ThunderFly-aerospace/TF-AEROSCALE/CAD/png/888_1001.png

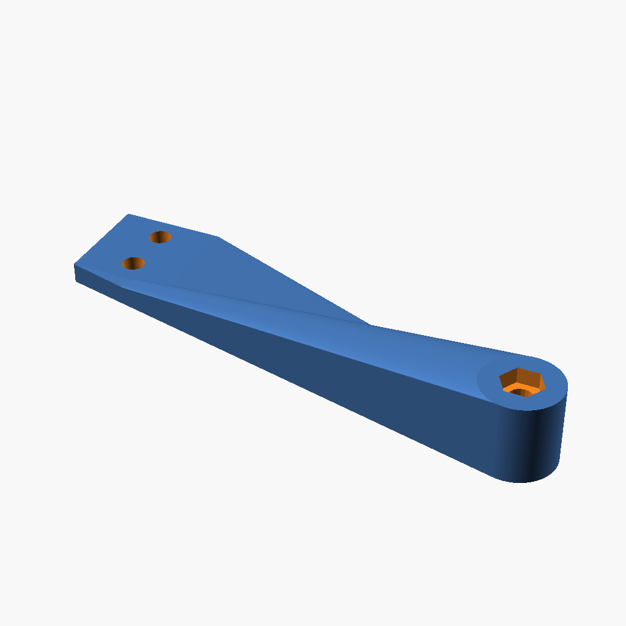
CAD/png/888_1001.png
