ThunderFly-aerospace/TF-AEROSCALE/CAD/png/888_1002.png

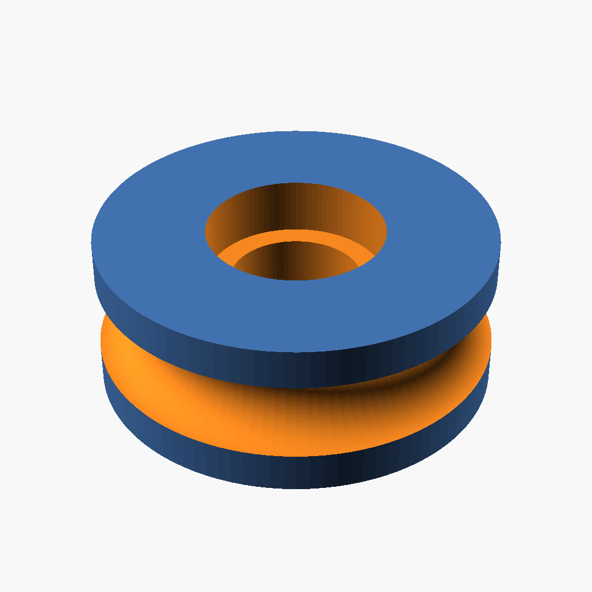
CAD/png/888_1002.png
