ThunderFly-aerospace/TF-AEROSCALE/CAD/png/888_3007.png

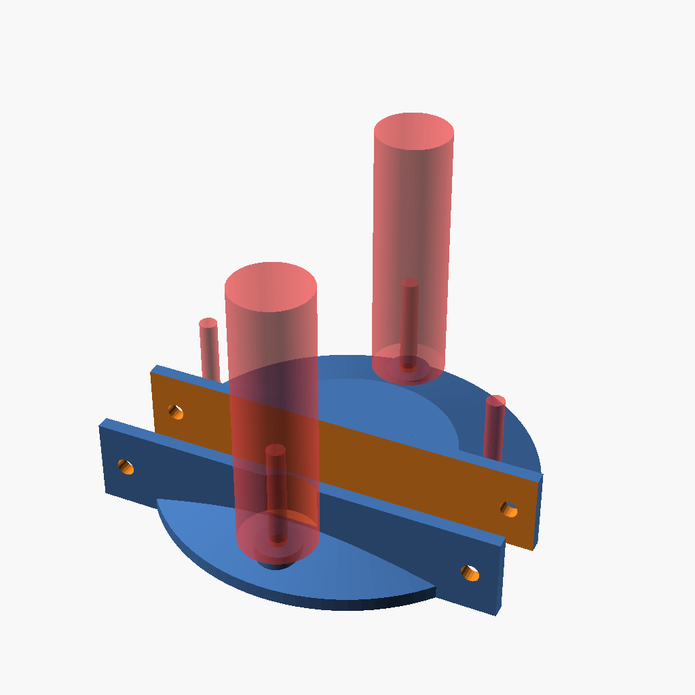
CAD/png/888_3007.png
