ThunderFly-aerospace/TF-AEROSCALE/CAD/png/888_5001.png

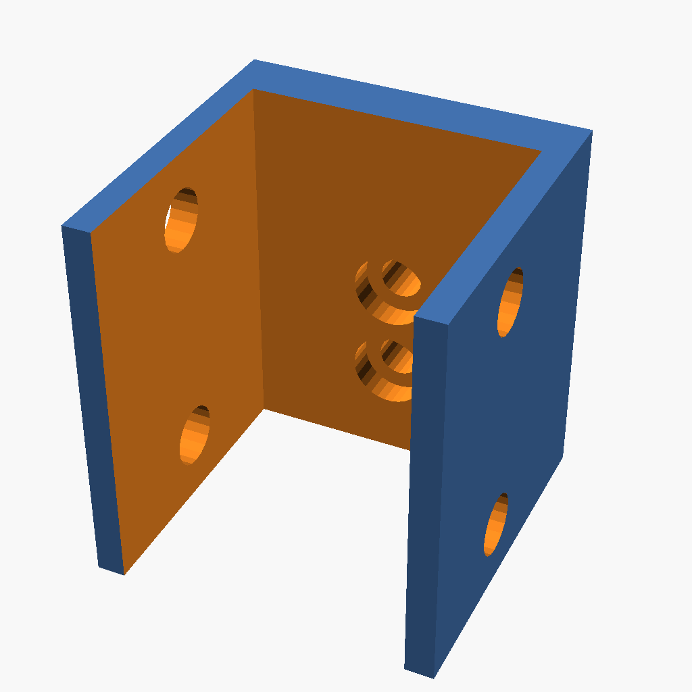
CAD/png/888_5001.png
