ThunderFly-aerospace/TF-AEROSCALE/CAD/png/888_5002.png

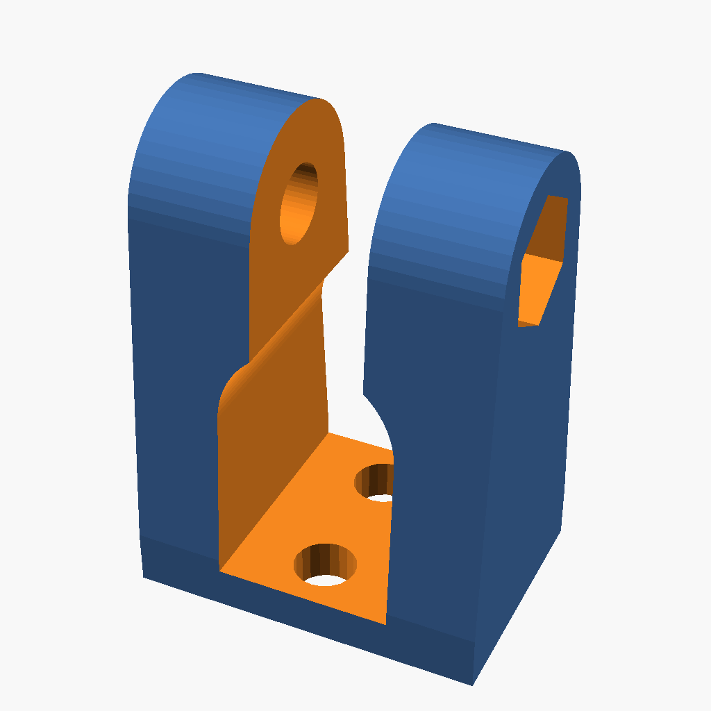
CAD/png/888_5002.png
