ThunderFly-aerospace/TF-AEROSCALE/CAD/png/888_5004.png

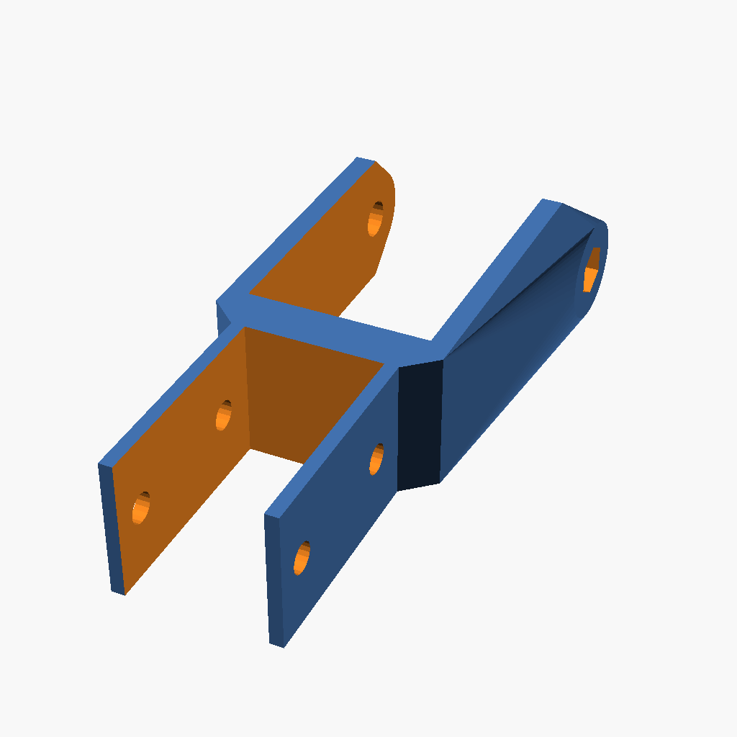
CAD/png/888_5004.png
