ThunderFly-aerospace/TF-AEROSCALE/CAD/png/888_5005.png

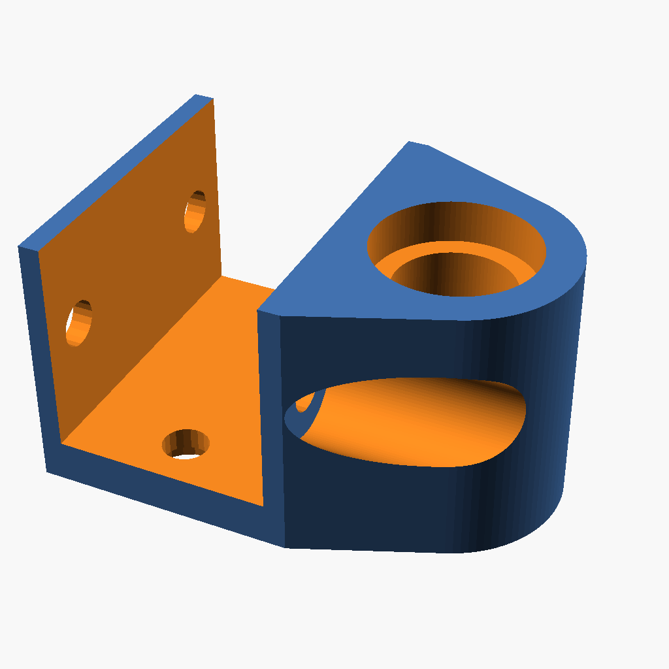
CAD/png/888_5005.png
