ThunderFly-aerospace/TF-AEROSCALE/CAD/png/888_5006.png

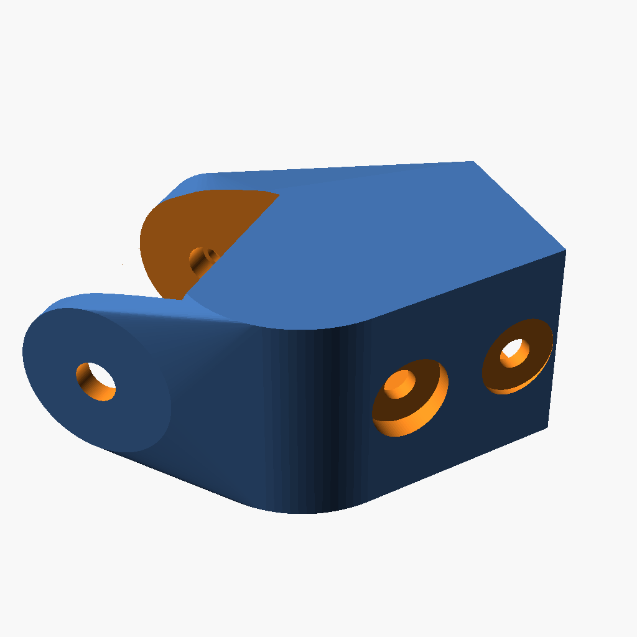
CAD/png/888_5006.png
