ThunderFly-aerospace/TF-AEROSCALE/CAD/png/888_5007.png

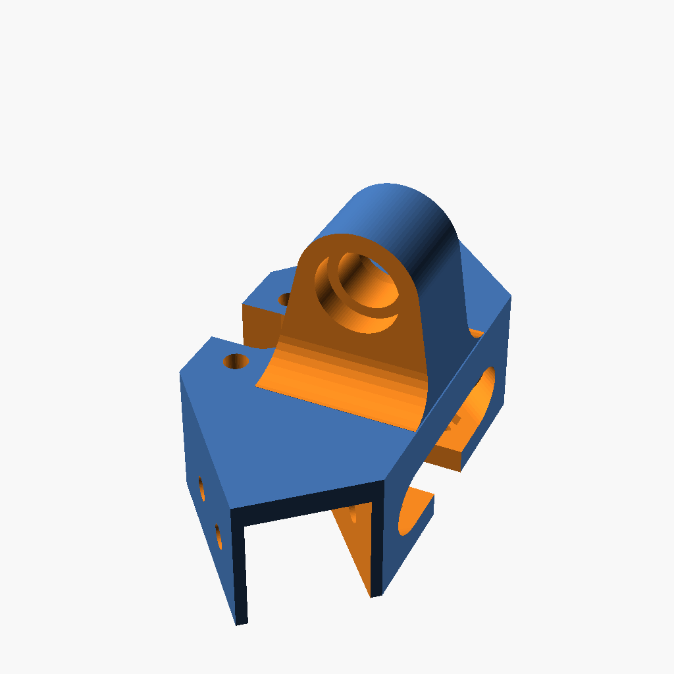
CAD/png/888_5007.png
