ThunderFly-aerospace/TF-AEROSCALE/CAD/png/888_5008.png

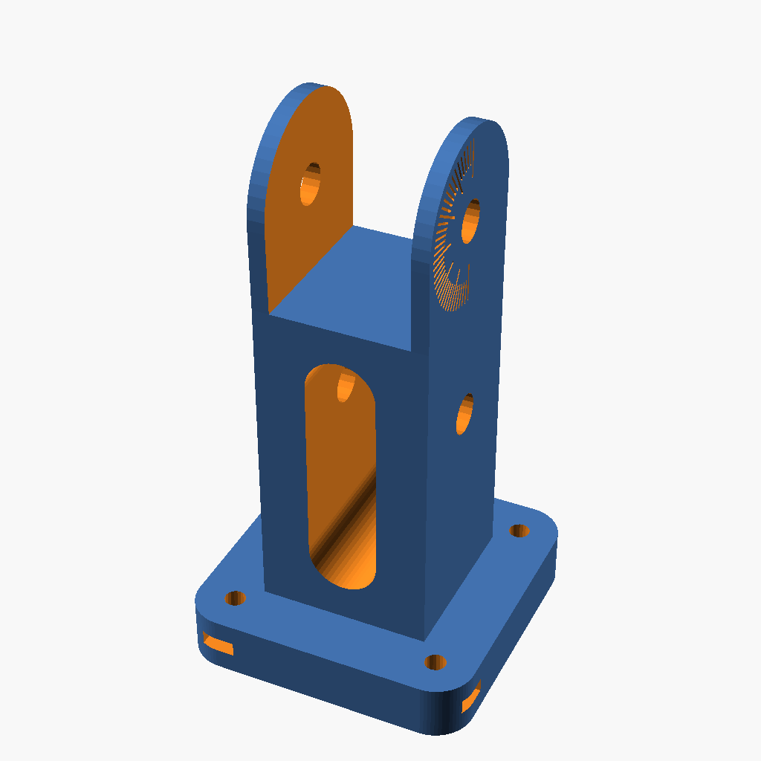
CAD/png/888_5008.png
