ThunderFly-aerospace/TF-AEROSCALE/CAD/png/888_5009.png

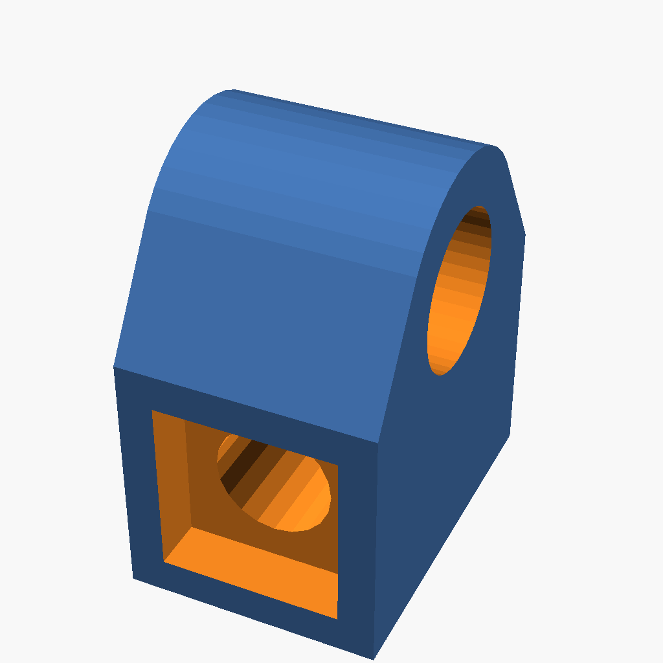
CAD/png/888_5009.png
