ThunderFly-aerospace/TF-AEROSCALE/CAD/png/888_5010.png

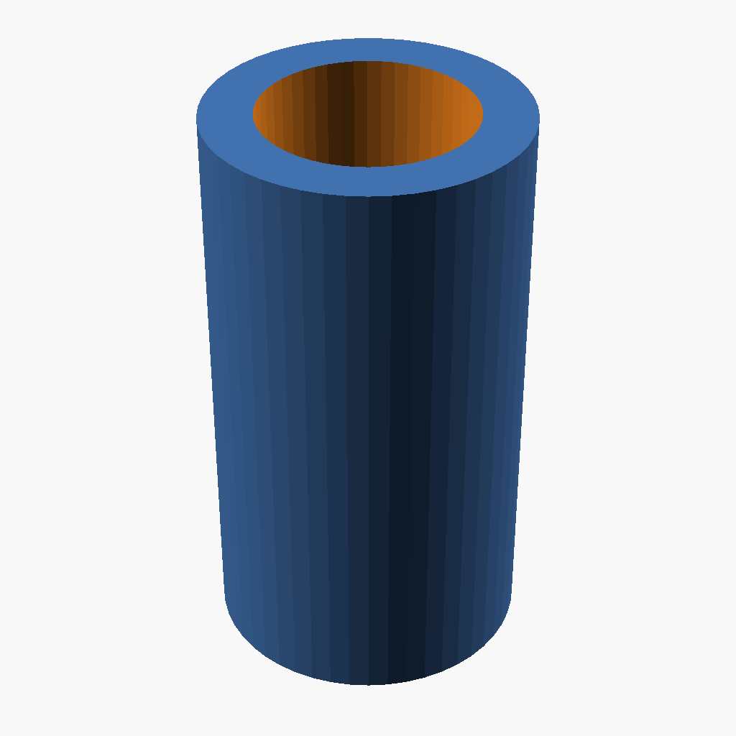
CAD/png/888_5010.png
