ThunderFly-aerospace/TF-AEROSCALE/CAD/png/888_5011.png

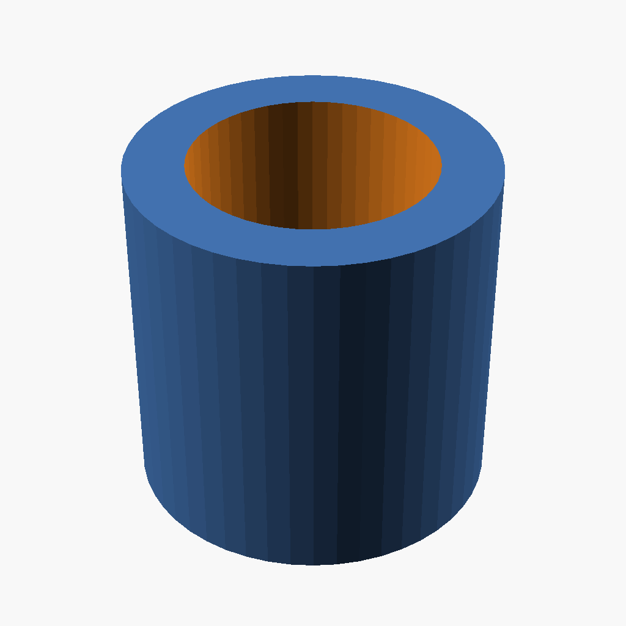
CAD/png/888_5011.png
