ThunderFly-aerospace/TF-AEROSCALE/CAD/png/888_5013.png

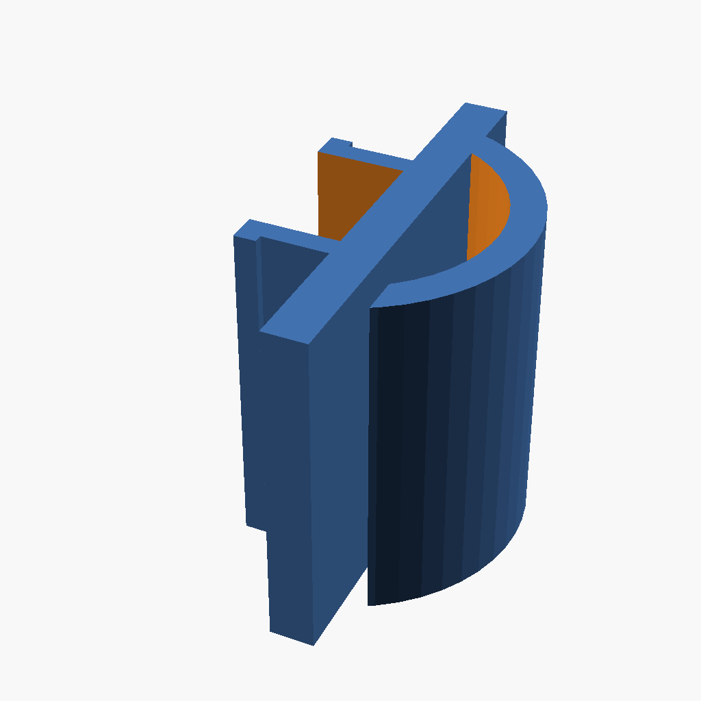
CAD/png/888_5013.png
