ThunderFly-aerospace/TF-AEROSCALE/CAD/png/888_5014_Front.png

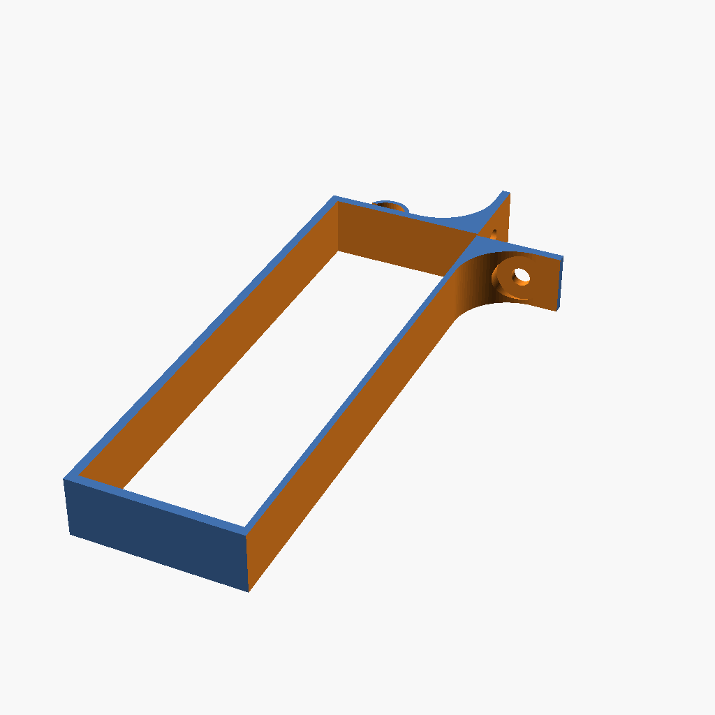
CAD/png/888_5014_Front.png
