ThunderFly-aerospace/TF-AEROSCALE/CAD/png/888_5015.png

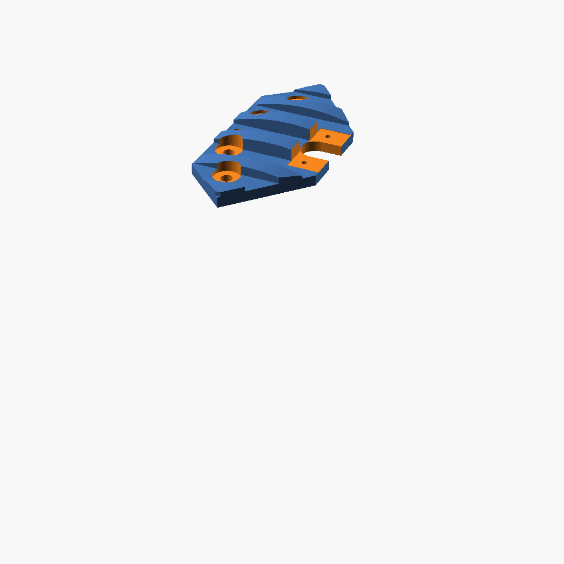
CAD/png/888_5015.png
