ThunderFly-aerospace/TF-AEROSCALE/CAD/amf/888_5012.amf

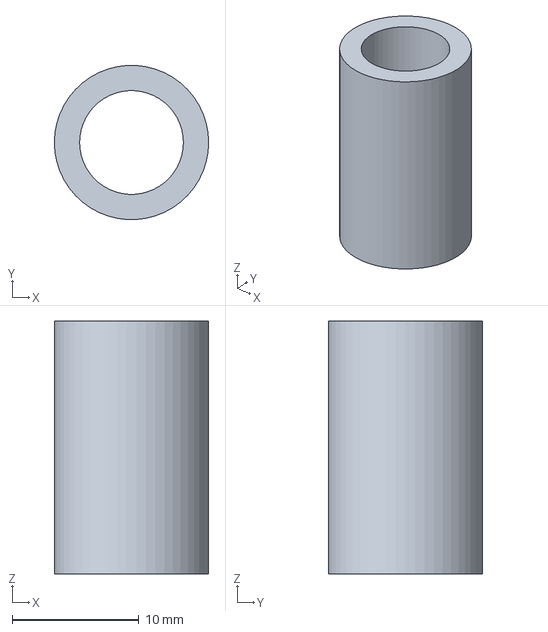
[picture p38: CAD file, 2021-09-10]
CAD/amf/888_5012.amf
12.2 x 12.2 x 20.0 mm
