ThunderFly-aerospace/TF-AEROSCALE/CAD/amf/888_5014_Back.amf

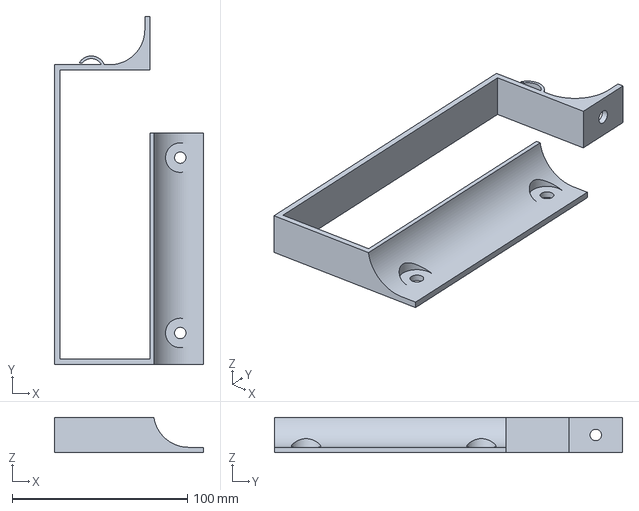
[picture p39: CAD file, 2021-09-10]
CAD/amf/888_5014_Back.amf
85.0 x 198.5 x 20.0 mm
