ThunderFly-aerospace/TF-AEROSCALE/CAD/amf/888_5010.amf

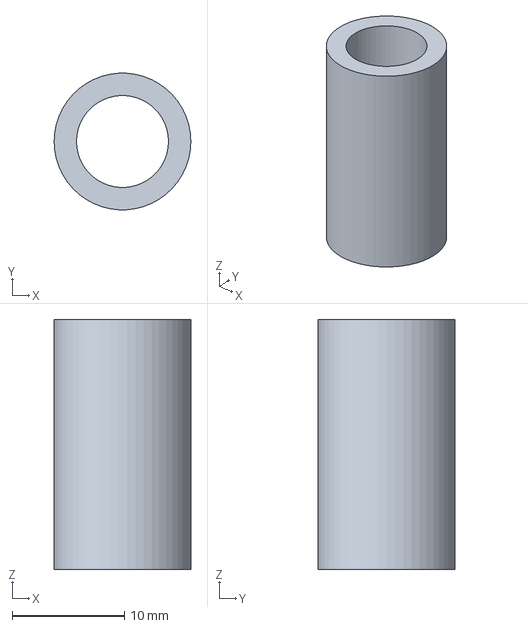
[picture p40: CAD file, 2021-09-10]
CAD/amf/888_5010.amf
12.2 x 12.2 x 22.3 mm
