ThunderFly-aerospace/TF-AEROSCALE/CAD/amf/888_5003_A.amf

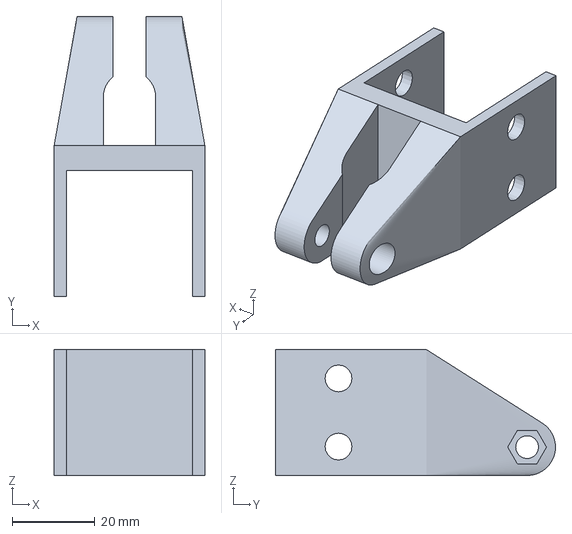
[picture p41: CAD file, 2021-09-10]
CAD/amf/888_5003_A.amf
36.5 x 67.8 x 30.5 mm
