ThunderFly-aerospace/TF-AEROSCALE/CAD/amf/888_1002.amf

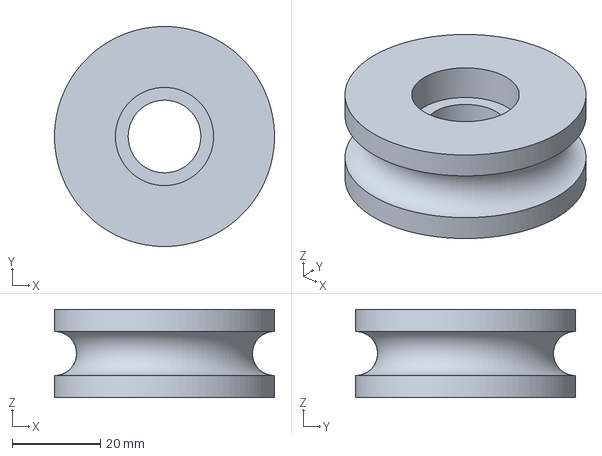
[picture p42: CAD file, 2021-09-10]
CAD/amf/888_1002.amf
50.0 x 50.0 x 20.0 mm
