ThunderFly-aerospace/TF-AEROSCALE/CAD/amf/888_1003.amf

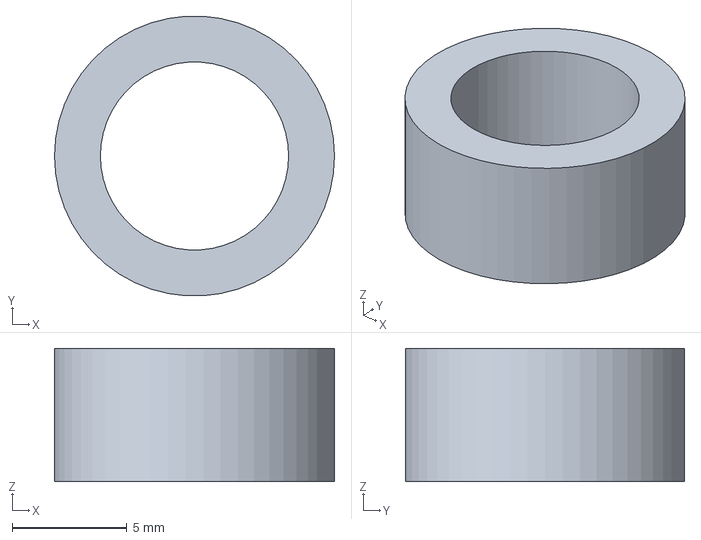
[picture p43: CAD file, 2021-09-10]
CAD/amf/888_1003.amf
12.2 x 12.2 x 5.80 mm
