ThunderFly-aerospace/TF-AEROSCALE/CAD/amf/888_5011.amf

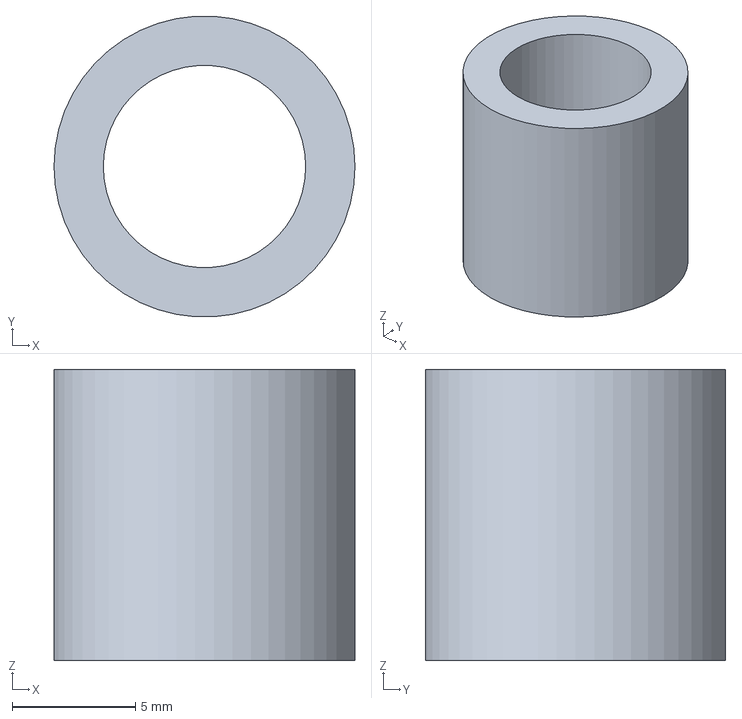
[picture p44: CAD file, 2021-09-10]
CAD/amf/888_5011.amf
12.2 x 12.2 x 11.8 mm
