ThunderFly-aerospace/TF-AEROSCALE/CAD/print_plates/888_1002.scad

//@set_slicing_config(../slicing/default.ini)

include <../parameters.scad>
use <../src/888_1002.scad>

888_1002(print_plate=true);
