ThunderFly-aerospace/TF-AEROSCALE/CAD/print_plates/888_3007.scad

//@set_slicing_config(../slicing/default.ini)

include <../parameters.scad>
use <../src/888_3007.scad>

888_3007();
