ThunderFly-aerospace/TF-AEROSCALE/CAD/print_plates/888_5002.scad

//@set_slicing_config(../slicing/default.ini)

include <../parameters.scad>
use <../src/888_5002.scad>

translate([0, 0, 4])
888_5002();
