ThunderFly-aerospace/TF-AEROSCALE/CAD/print_plates/888_5003_A.scad

//@set_slicing_config(../slicing/default.ini)

include <../parameters.scad>
use <../src/888_5003.scad>

888_5003_A();
