ThunderFly-aerospace/TF-AEROSCALE/CAD/print_plates/888_5005.scad

//@set_slicing_config(../slicing/default.ini)

include <../parameters.scad>
use <../src/888_5005.scad>

rotate([-90, 0, 0])
888_5005(true);
