ThunderFly-aerospace/TF-AEROSCALE/CAD/print_plates/888_5008.scad

//@set_slicing_config(../slicing/default.ini)

include <../parameters.scad>
use <../src/888_5008.scad>

translate([0, 0, 10])
888_5008(true);
