ThunderFly-aerospace/TF-AEROSCALE/CAD/print_plates/888_5014_Front.scad

//@set_slicing_config(../slicing/default.ini)

include <../parameters.scad>
use <../src/888_5014.scad>

rotate([0, -90, 0])
888_5014_front();
