ThunderFly-aerospace/TF-AEROSCALE/CAD/print_plates/TF_G2_rotor_adapter.scad

//@set_slicing_config(../slicing/default.ini)

include <../parameters.scad>
use <../src/TF_G2_rotor_adapter.scad>


translate([0, 0, 14.5])
rotate([0, -90, 0])
TF_G2_rotor_adapter();
