ThunderFly-aerospace/TF-AEROSCALE/CAD/src/888_4008.scad

include <../parameters.scad>
include <lib/polyScrewThread_r1.scad>

module 888_4008(draft = true){

// TODO: Je potreba procistit parametry, po predelani na spulku zde urcite mnoho parametru je nevyuzitych. Pripadne je okomentovat. [Roman, 2020/11]

    angle_between_blades = 360 / rotor_blades_count;

    //shaft_diameter = 6.1;
    thickness = 2.3;
    top_thickness = 3;
    //blade_screws_distance = (16.47+11.86)/2;

    height_from_rotor_nut = 27.5 - 1.65 ;

    // %cylinder(d = 5, h = height_from_rotor_nut);

    rotor_center_r=12 + 1;
    edge_distance_from_center = 7.5;
    spacer_disc_diameter = 3 * M3_screw_diameter;
    spare_disc_height = 0.6;

    starter_top_r=14;
    starter_top_h=M3_screw_head_height+3;
    starter_pipe_d_top = 20;
    starter_pipe_d_middle = 35;
    starter_pipe_d_bottom = 20;
    starter_neck_r=10;
    starter_neck_h=1;
    starter_bottom_h=5;
    starter_rope_diameter=2;

    starter_rope_d = 39.2;

    sensor_cap_height=starter_top_h+starter_neck_h+starter_bottom_h;

    rpm_sensor_inner_r=12.5;
    rpm_sensor_thickness = 1.3;
    rpm_sensor_h = height_from_rotor_nut - starter_top_h;
    rpm_sensor_base_h= 2;
    rpm_sensor_count=16;
    rpm_hole_h = 50;
    //rpm_hole_width = 7;

    screws_head_d=7;
    screws_h=14;



    translate([0,0,-top_thickness])
        rotate([0,0, rotor_delta_angle]) {
            difference() {
                union(){
                    difference()
                    {
                            union()
                            {
                                cylinder(r1 = rotor_center_r, d2=starter_rope_d, h = top_thickness+starter_top_h, $fn = draft?rpm_sensor_count:120);
                                translate([0,0, top_thickness + starter_top_h])
                                    cylinder(h=rpm_sensor_h, d=starter_rope_d + starter_rope_diameter, $fn=draft?rpm_sensor_count:120);
                            }

                          difference(){
                            translate([0,0,top_thickness])
                                  cylinder(h=sensor_cap_height/2 + M3_nut_height, d1=starter_pipe_d_top - top_thickness, d2 = starter_pipe_d_middle, $fn=draft?rpm_sensor_count:120);
                            hull(){
                            translate([0,0,top_thickness])
                                  cylinder(h=M3_nut_height, d1=M3_nut_diameter*2, d2 = M3_nut_diameter * 1.2, $fn=draft?rpm_sensor_count:120);
                            translate([0, 0, top_thickness])
                                  cube([M3_nut_diameter, starter_rope_d, M3_nut_height], center=true);
                            }
                            for (i = [1:rotor_blades_count]){
                                rotate([0, 0, i*angle_between_blades + angle_between_blades/2 + 180])
                                    translate([0, edge_distance_from_center+15/2, -10/2+thickness/2])
                                    {
                                        translate([0,-9,6.6])
                                            rotate([atan2(starter_top_h,(16-edge_distance_from_center)),0,0])
                                                translate([-14,0,-10])
                                                    cube([30,15,10]);
                                    }
                            }

                          }
                          translate([0,0,top_thickness + M3_nut_height + sensor_cap_height/2])
                                cylinder(h=sensor_cap_height*0.7, d1=starter_pipe_d_middle, d2 = starter_pipe_d_middle, $fn=draft?rpm_sensor_count:120);
                          translate([0,0,top_thickness + M3_nut_height + 1.2*sensor_cap_height])
                                cylinder(h=sensor_cap_height, d1=starter_pipe_d_middle, d2 = starter_pipe_d_bottom, $fn=draft?rpm_sensor_count:120);
                    }
                }

              //hex_screw(15,4,55,30,1.5,2,24,8,0,0);
              // Zavit pro namotani provazku
              translate([0, 0, top_thickness]) difference(){
                  cylinder(d = starter_rope_d+10, h = rpm_sensor_h + starter_top_h);
                  if(draft){
                    color("gray") cylinder(d = starter_rope_d, h = rpm_sensor_h + starter_top_h);
                  }else{
                      screw_thread(starter_rope_d, starter_rope_diameter, 45, rpm_sensor_h + starter_top_h, draft?5:PI/3, -2);
                  }
                  // light blocking rim
                  translate([0, 0, rpm_sensor_h + starter_top_h - 1.5*starter_rope_diameter])
                      cylinder(d1 = starter_pipe_d_middle, d2 = starter_rope_d+starter_rope_diameter/2, h = starter_rope_diameter, $fn = draft?rpm_sensor_count:120);
                  translate([0, 0, rpm_sensor_h + starter_top_h - starter_rope_diameter/2])
                      cylinder(d = starter_rope_d+starter_rope_diameter/2, h = starter_rope_diameter, $fn = draft?rpm_sensor_count:120);
              }
              /*
               * Just a 100mm long threaded rod.
               *
               * screw_thread(15,   // Outer diameter of the thread
               *               4,   // Step, traveling length per turn, also, tooth height, whatever...
               *              55,   // Degrees for the shape of the tooth
               *                       (XY plane = 0, Z = 90, btw, 0 and 90 will/should not work...)
               *             100,   // Length (Z) of the tread
               *            PI/2,   // Resolution, one face each "PI/2" mm of the perimeter,
               *               0);  // Countersink style:
               *                         -2 - Not even flat ends
               *                         -1 - Bottom (countersink'd and top flat)
               *                          0 - None (top and bottom flat)
               *                          1 - Top (bottom flat)
               *                          2 - Both (countersink'd)
               */
              // screw_thread(15,4,55,100,PI/2,2);

              // Otvor na zastrceni provazku
              translate([0, 0, starter_top_h+top_thickness + rpm_sensor_h -1.65 ])
                  rotate([-90, 0, -rotor_delta_angle - 45])
                    cylinder(d = starter_rope_diameter, h = 50, center = false, $fn = 10);

              // Cut for rope fix before start
              rotate([0, 0, 180])
                 translate([-starter_pipe_d_middle/2, starter_pipe_d_top/2 + (starter_pipe_d_middle/2 - starter_pipe_d_top/2)/2, starter_top_h - starter_top_h/3])
                    rotate([30, 3, 0])
                      cube([starter_pipe_d_middle, starter_pipe_d_middle, starter_rope_diameter]);


              // Otvory pro senzor
              translate([0,0,top_thickness + M3_nut_height + sensor_cap_height])
                intersection() {
                    union(){  // sensor teeth outer rim
                      cylinder(d = starter_pipe_d_middle, h = rpm_hole_h/4, $fn = draft?rpm_sensor_count:120);
                      translate([0, 0, - M3_nut_height - sensor_cap_height + rpm_sensor_h + starter_top_h - starter_rope_diameter])
                        cylinder(d1 = starter_pipe_d_middle, d2 = starter_rope_d - starter_rope_diameter/2, h = starter_rope_diameter, $fn = draft?rpm_sensor_count:120);
                    }

                    for (i=[0:rpm_sensor_count]) rotate([0, 0, (360/rpm_sensor_count)*i]){
                        linear_extrude(height = rpm_hole_h)
                        polygon(points=[[0,0],[starter_rope_d/2, ((starter_rope_d/2) * sin(360/rpm_sensor_count/2))/2], [starter_rope_d/2, -((starter_rope_d/2) * sin(360/rpm_sensor_count/2))/2]]);
                    }
                }

              // rotor axis
              cylinder(d = M3_screw_diameter+0.1, h = 3* thickness+starter_top_h, center = true, $fn = 20);
              // Rotor nut
              translate([0, 0, -0.1]) cylinder(d = M3_nut_diameter, h = 6+0.2, $fn = 6);


              // Odecneni bocnych srazenych hran, Odecteni kapes pro matky
              translate([0, 0, thickness/2])
                for (i = [1:rotor_blades_count]){
                  rotate([0, 0, i*angle_between_blades + angle_between_blades/2 + 180])
                      translate([0, edge_distance_from_center+15/2, -10/2+thickness/2])
                      {
                          cube([30, 15, 10], center = true);
                          translate([0,-7.5,5])
                              rotate([atan2(starter_top_h,(16-edge_distance_from_center)),0,0])
                                  translate([-15,0,-10])
                                      cube([30,15,10]);
                      }
                  angle=(rotor_blades_count/2 == round(rotor_blades_count/2))? (i*angle_between_blades):i*angle_between_blades - angle_between_blades/2;
                  rotate([0,0, angle])
                  {
                      // Two screw holes around rotor axis
                    translate([0, 3 + 4.5 + blade_mount_screw/2, -5])
                      cylinder(d = blade_mount_screw, h = 8, $fn = 20);
                    translate([0, 3 + 4.5 + blade_mount_screw/2, 4])   // Tloušťka pomocné ucpávky v místě díry pro šroub je asi 0.35 mm (pro z = 3.6 už vede díra skrz)
                      cylinder(d = blade_mount_screw, h = 4, $fn = 20);

                    translate([0, 3 + 4.5 + blade_mount_screw/2, screws_h/2+thickness/2-7])
                      cylinder(d = M3_nut_diameter, h = 2.5, $fn = 6);
                    translate([0, 3 + 4.5 + blade_mount_screw/2+4, screws_h/2+thickness/2-7+2.5/2])
                      cube([M3_nut_diameter, 8  ,  2.5], center = true);


                  }

              }
              // cross section for model construction
              //translate([-50,0,0])cube(100);

            }
        }
}


888_4008($preview);
