ThunderFly-aerospace/TF-AEROSCALE/CAD/slicing/3dprinter_configs/src/models/kryt.ini

bottom_solid_layers = 0
external_perimeter_extrusion_width = 0.8
external_perimeter_speed = 30
extra_perimeters = 0
extrusion_multiplier = 1
extrusion_width = 0.8
first_layer_extrusion_width = 0.8
first_layer_height = 0.18
first_layer_speed = 15
layer_height = 0.18
min_shell_thickness = 1.8
min_top_bottom_shell_thickness = 0
only_retract_when_crossing_perimeters = 1
perimeter_extrusion_width = 0.8
perimeter_speed = 30
perimeters = 2
top_solid_layers = 0
