ThunderFly-aerospace/TF-AEROSCALE/software/spidevWraper.py

#!/usr/bin/python3

import spidev

class SPIWraper:
    def __init__(self,cs_pin):
        self.spi=spidev.SpiDev()
        self.spi.open(0,cs_pin)

        self.spi.max_speed_hz=400000
        self.spi.mode=1

        self.result=[];

    def SPI_write(self,cs,data):
        '''write data to bus with selected CS pin'''
        tmpresult = self.spi.xfer2(data)
        self.result=[x for x in tmpresult]

    def SPI_read(self,num_bytes):
        '''read result from last transaction'''
        return self.result;
