ThunderFly-aerospace/TF-AEROSCALE/software/1_scale_calibration_spidev.py

#!/usr/bin/python3
import sys
import time

from BRIDGEADC01 import BRIDGEADC01
from spidevWraper import SpiWrapper

def doCalibration(scale, channel):

    scale.doCalibration(channel)
    offset=scale.getOffsetRegister();
    gain=scale.getFullScaleRegister();
    weight=scale.getUnitCalibrationGain();

    return [offset,gain,weight]

print("1 Weight scale configuration.. calibration of 1 weights connected to single spidev  calibrate first channel of weights ")

spi0 = SPIWraper(0)

scale1 = BRIDGEADC01(spi0,0,1)
scale1.reset()
freq=scale1.setFilterAC(200)
sys.stdout.write("frekvence vyčítání: %4.2f;\n" %(freq))
sys.stdout.flush()


sys.stdout.write("\n\n\nScale 0:\n\n\n")
sys.stdout.flush()
weight0=doCalibration(scale1,0)

f=open("1ScaleCalibration.txt","w")
f.write("%d %d %g\n" % tuple(weight0) )
f.close()
